benedictemarty/ulx3s_oric/ecran.png

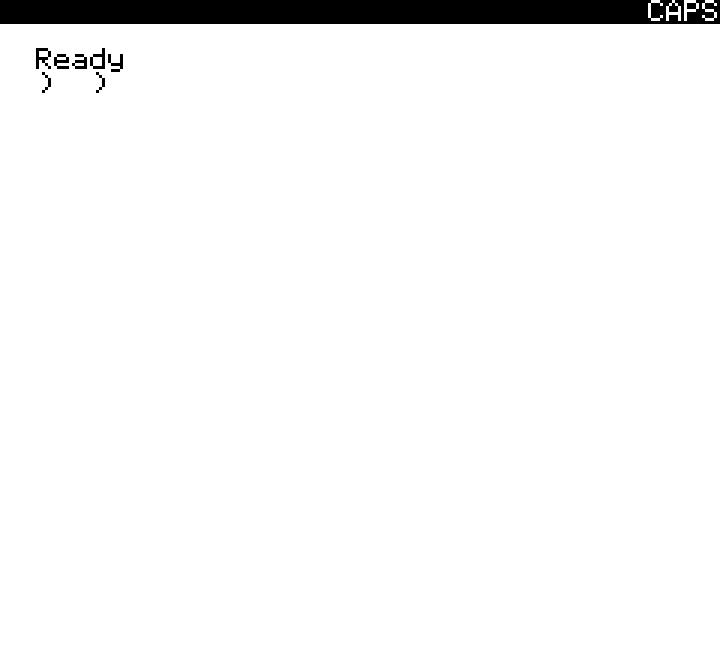
ecran.png
