benedictemarty/ulx3s_oric/hardware/phaseA/render_full.png

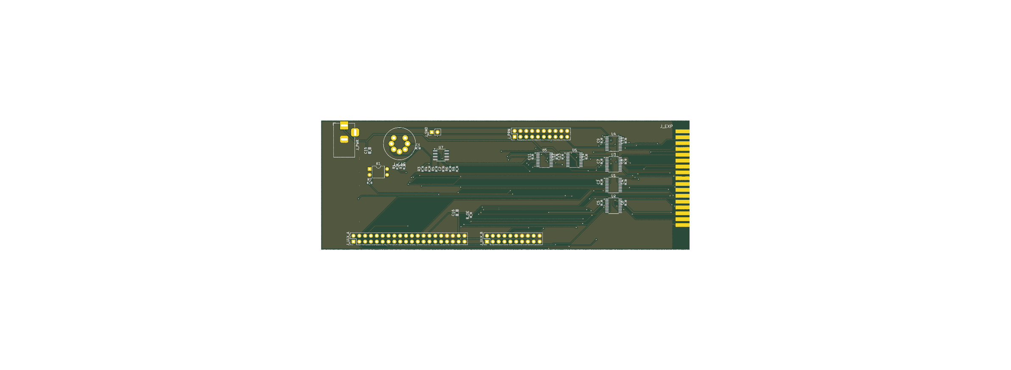
hardware/phaseA/render_full.png
