benedictemarty/ulx3s_oric/hardware/phaseA/vue3d_1.png

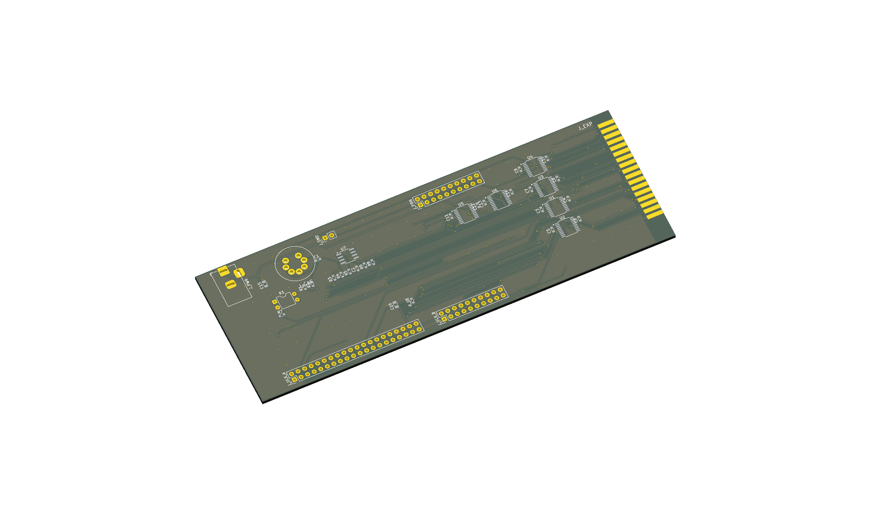
hardware/phaseA/vue3d_1.png
