benedictemarty/ulx3s_oric/hardware/phaseA/vue3d_peigne.png

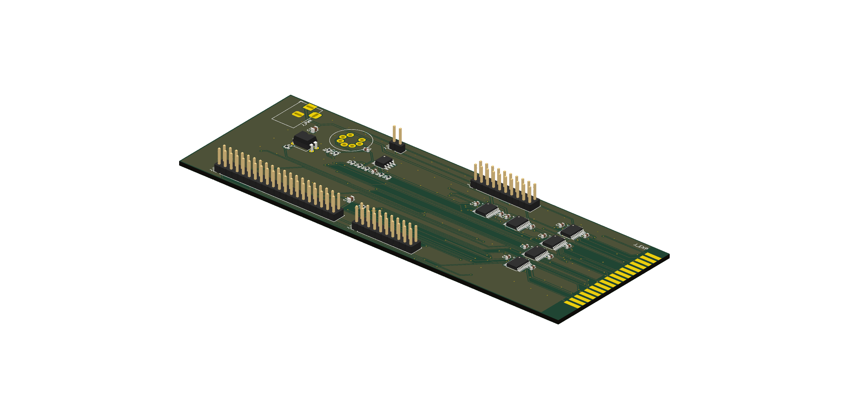
hardware/phaseA/vue3d_peigne.png
