benedictemarty/ulx3s_oric/rtl/pll_sys.v

// diamond 3.7 accepts this PLL
// diamond 3.8-3.9 is untested
// diamond 3.10 or higher is likely to abort with error about unable to use feedback signal
// cause of this could be from wrong CPHASE/FPHASE parameters
module pll_sys
(
    input clkin, // 25 MHz, 0 deg
    output clkout0, // 25 MHz, 0 deg
    output clkout1, // 12 MHz, 0 deg
    output locked
);
(* FREQUENCY_PIN_CLKI="25" *)
(* FREQUENCY_PIN_CLKOP="25" *)
(* FREQUENCY_PIN_CLKOS="12" *)
(* ICP_CURRENT="12" *) (* LPF_RESISTOR="8" *) (* MFG_ENABLE_FILTEROPAMP="1" *) (* MFG_GMCREF_SEL="2" *)
EHXPLLL #(
        .PLLRST_ENA("DISABLED"),
        .INTFB_WAKE("DISABLED"),
        .STDBY_ENABLE("DISABLED"),
        .DPHASE_SOURCE("DISABLED"),
        .OUTDIVIDER_MUXA("DIVA"),
        .OUTDIVIDER_MUXB("DIVB"),
        .OUTDIVIDER_MUXC("DIVC"),
        .OUTDIVIDER_MUXD("DIVD"),
        .CLKI_DIV(1),
        .CLKOP_ENABLE("ENABLED"),
        .CLKOP_DIV(24),
        .CLKOP_CPHASE(11),
        .CLKOP_FPHASE(0),
        .CLKOS_ENABLE("ENABLED"),
        .CLKOS_DIV(50),
        .CLKOS_CPHASE(11),
        .CLKOS_FPHASE(0),
        .FEEDBK_PATH("CLKOP"),
        .CLKFB_DIV(1)
    ) pll_i (
        .RST(1'b0),
        .STDBY(1'b0),
        .CLKI(clkin),
        .CLKOP(clkout0),
        .CLKOS(clkout1),
        .CLKFB(clkout0),
        .CLKINTFB(),
        .PHASESEL0(1'b0),
        .PHASESEL1(1'b0),
        .PHASEDIR(1'b1),
        .PHASESTEP(1'b1),
        .PHASELOADREG(1'b1),
        .PLLWAKESYNC(1'b0),
        .ENCLKOP(1'b0),
        .LOCK(locked)
	);
endmodule
